andrenho/fortuna-io-board/schematic/pi-pico-vga.kicad_sch

## KiCad design schematic/pi-pico-vga.kicad_sch (2025-08-25)

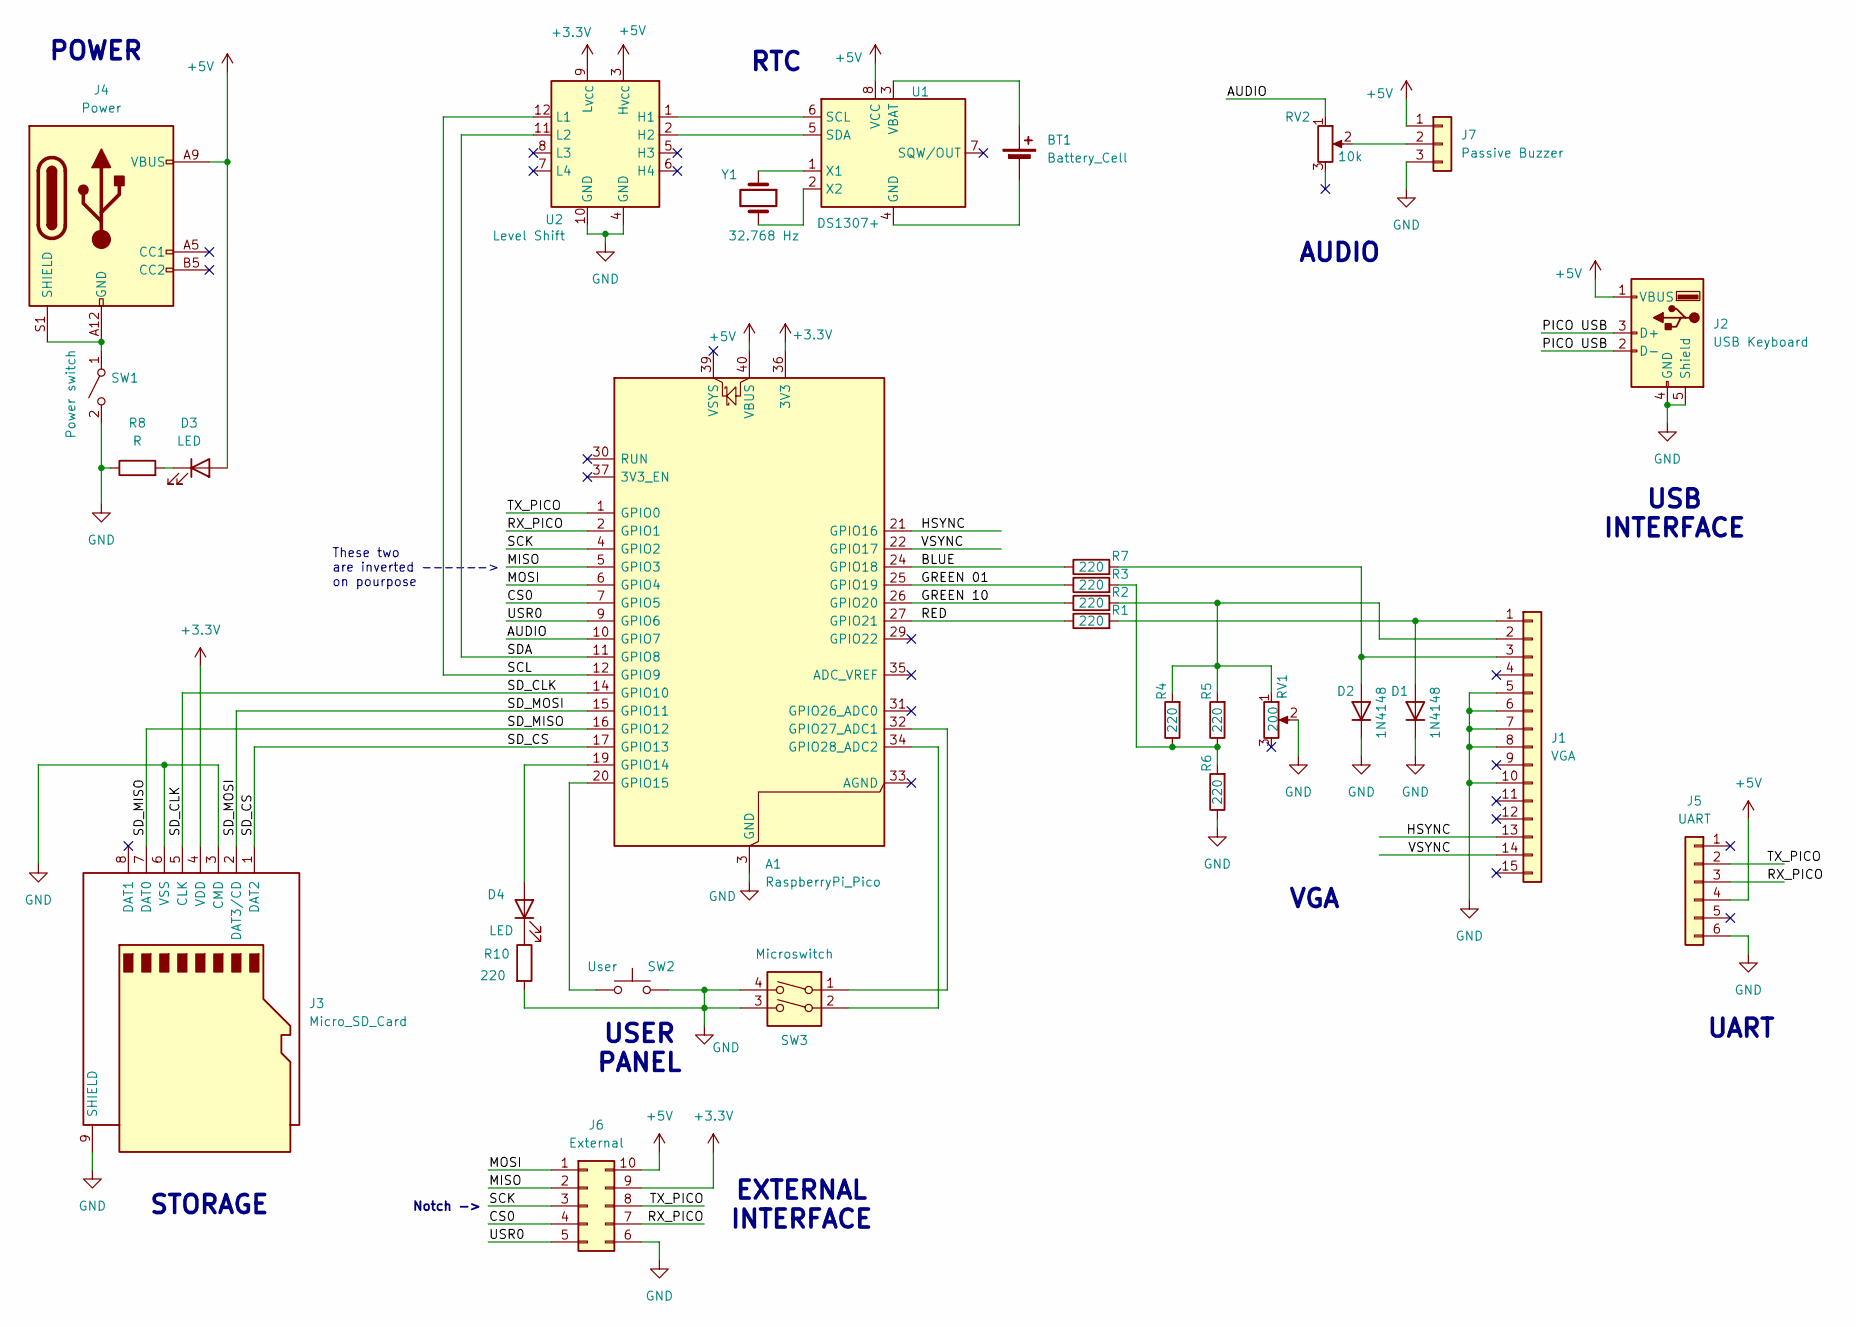
[picture p6: schematic pi-pico-vga.kicad_sch]

Parts:
A1: RaspberryPi_Pico; RaspberryPi_Pico_Common_Unspecified
BT1: Battery_Cell
D1, D2: 1N4148; D_DO-35_SOD27_P7.62mm_Horizontal
D3, D4: LED
J1: VGA
J2: USB Keyboard
J3: Micro_SD_Card
J4: Power
J5: UART
J6: External
J7: Passive Buzzer
R1, R2, R3, R4, R5, R6, R7, R10: 220
R8: R
RV1: 200
RV2: 10k
SW1: Power switch
SW2: User
SW3: Microswitch
U1: DS1307+; DIP-8_W7.62mm
U2: Level Shift; SOIC-14_3.9x8.7mm_P1.27mm
Y1: 32.768 Hz

Connections:
+3.3V: A1.36 (3V3), J3.4 (VDD), J6.9, U2.9 (NC)
+5V: A1.40 (VBUS), D3.2 (A), J2.1 (VBUS), J4.A9 (VBUS), J4.B9 (VBUS), J5.4, J6.10, J7.1, U1.8 (VCC), U2.3 (H_{VCC})
AUDIO: A1.10 (GPIO7), RV2.1
BLUE: A1.24 (GPIO18), R7.1
CS0: A1.7 (GPIO5), J6.4
GND: A1.3 (GND), A1.8 (GND), A1.13 (GND), A1.18 (GND), A1.23 (GND), A1.28 (GND), A1.38 (GND), D1.1 (K), D2.1 (K), J1.5, J1.6, J1.7, J1.8, J1.10, J2.4 (GND), J2.5 (Shield), J3.3 (CMD), J3.6 (VSS), J3.9 (SHIELD), J5.6, J6.6, J7.3, R6.1, R8.1, R10.2, RV1.2, SW1.2 (B), SW2.2, SW3.3, SW3.4, U2.4 (GND), U2.10 (GND)
GREEN 01: A1.25 (GPIO19), R3.1
GREEN 10: A1.26 (GPIO20), R2.1
HSYNC: A1.21 (GPIO16), J1.13
MISO: A1.5 (GPIO3), J6.2
MOSI: A1.6 (GPIO4), J6.1
unnamed: A1.19 (GPIO14), D4.2 (A)
unnamed: A1.20 (GPIO15), SW2.1
unnamed: A1.32 (GPIO27_ADC1), SW3.1
unnamed: A1.34 (GPIO28_ADC2), SW3.2
unnamed: BT1.1 (+), U1.3 (VBAT)
unnamed: BT1.2 (-), U1.4 (GND)
unnamed: D1.2 (A), J1.1, R1.2
unnamed: D2.2 (A), J1.3, R7.2
unnamed: D3.1 (K), R8.2
unnamed: D4.1 (K), R10.1
unnamed: J1.2, R2.2, R4.2, R5.2, RV1.1
unnamed: J4.A12 (GND), J4.B12 (GND), J4.S1 (SHIELD), SW1.1 (A)
unnamed: J7.2, RV2.2
unnamed: R3.2, R4.1, R5.1, R6.2
unnamed: U1.1 (X1), Y1.1
unnamed: U1.2 (X2), Y1.2
unnamed: U1.5 (SDA), U2.2 (H2)
unnamed: U1.6 (SCL), U2.1 (H1)
PICO USB: J2.2 (D-), J2.3 (D+)
RED: A1.27 (GPIO21), R1.1
RX_PICO: A1.2 (GPIO1), J5.3, J6.7
SCK: A1.4 (GPIO2), J6.3
SCL: A1.12 (GPIO9), U2.12 (L1)
SDA: A1.11 (GPIO8), U2.11 (L2)
SD_CLK: A1.14 (GPIO10), J3.5 (CLK)
SD_CS: A1.17 (GPIO13), J3.1 (DAT2)
SD_MISO: A1.16 (GPIO12), J3.7 (DAT0)
SD_MOSI: A1.15 (GPIO11), J3.2 (DAT3/CD)
TX_PICO: A1.1 (GPIO0), J5.2, J6.8
USR0: A1.9 (GPIO6), J6.5
VSYNC: A1.22 (GPIO17), J1.14

Notes on the sheet:
UART
USB INTERFACE
AUDIO
STORAGE
VGA
POWER
EXTERNAL INTERFACE
USER PANEL
Notch ->
RTC
These two are inverted ------> on pourpose
